johaa1993/PDB/PDB5/address_1.PNG

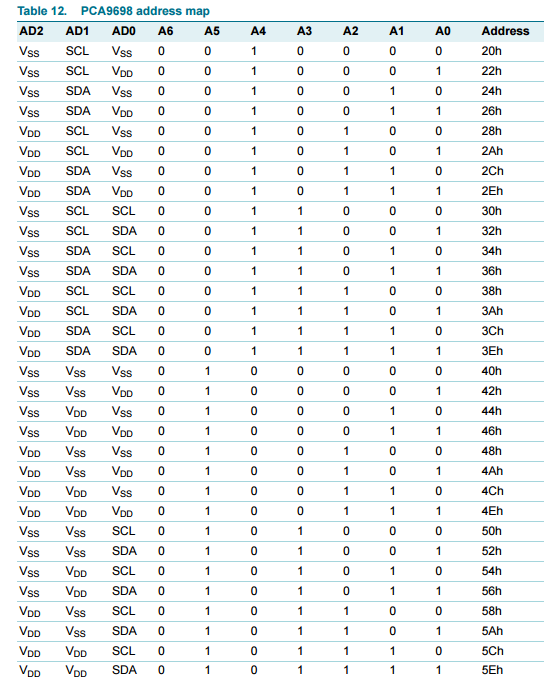
PDB5/address_1.PNG
