johaa1993/PDB/PDB5/Capture2.PNG

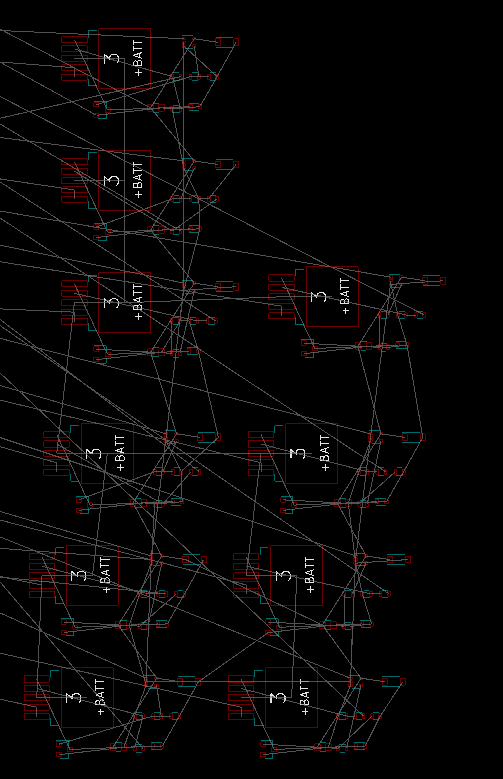
PDB5/Capture2.PNG
