johaa1993/PDB/PDB5/Capture.PNG

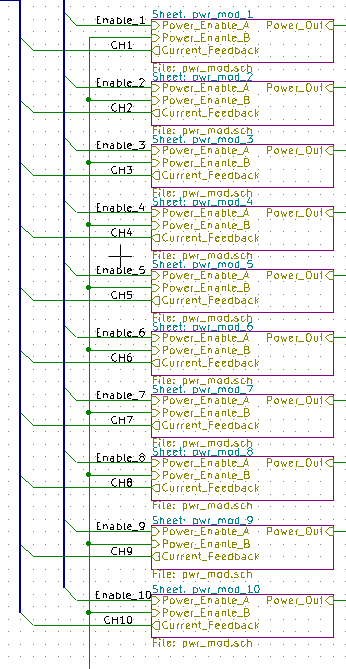
PDB5/Capture.PNG
