johaa1993/PDB/AUIPS7111S/main.kicad_pcb

## KiCad design AUIPS7111S/main.kicad_pcb (2016-11-23)

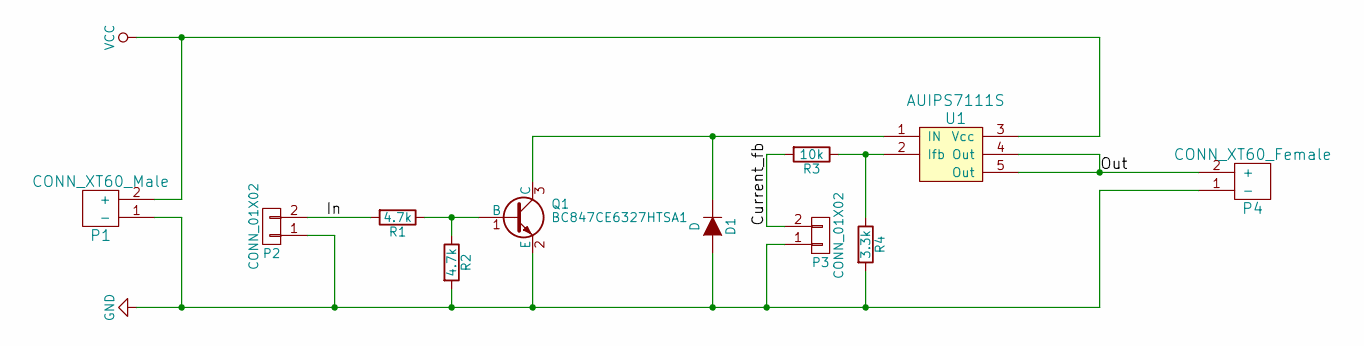
[picture p43: schematic main.sch]

Parts:
D1: D; Diode_DO-35_SOD27_Horizontal_RM10
P1: CONN_XT60_Male; CONN_XT60_Male1_Horizontal
P2, P3: CONN_01X02; Pin_Header_Straight_1x02
P4: CONN_XT60_Female; CONN_XT60_Female_Horizontal
Q1: BC847CE6327HTSA1; SOT-23
R1, R2: 4.7k; Resistor_Horizontal_RM7mm
R3: 10k; Resistor_Horizontal_RM7mm
R4: 3.3k; Resistor_Horizontal_RM7mm
U1: AUIPS7111S; TO-263-5Lead

Connections:
/Current_fb: P3.2, R3.2
/In: P2.2, R1.2
/Out: P4.2 (+), U1.4 (Out), U1.5 (Out)
GND: D1.2 (A), P1.1 (-), P2.1, P3.1, P4.1 (-), Q1.2 (E), R2.2, R4.2
unnamed: D1.1 (K), Q1.3 (C), U1.1 (IN)
unnamed: Q1.1 (B), R1.1, R2.1
unnamed: R3.1, R4.1, U1.2 (Ifb)
VCC: P1.2 (+), U1.3 (Vcc)

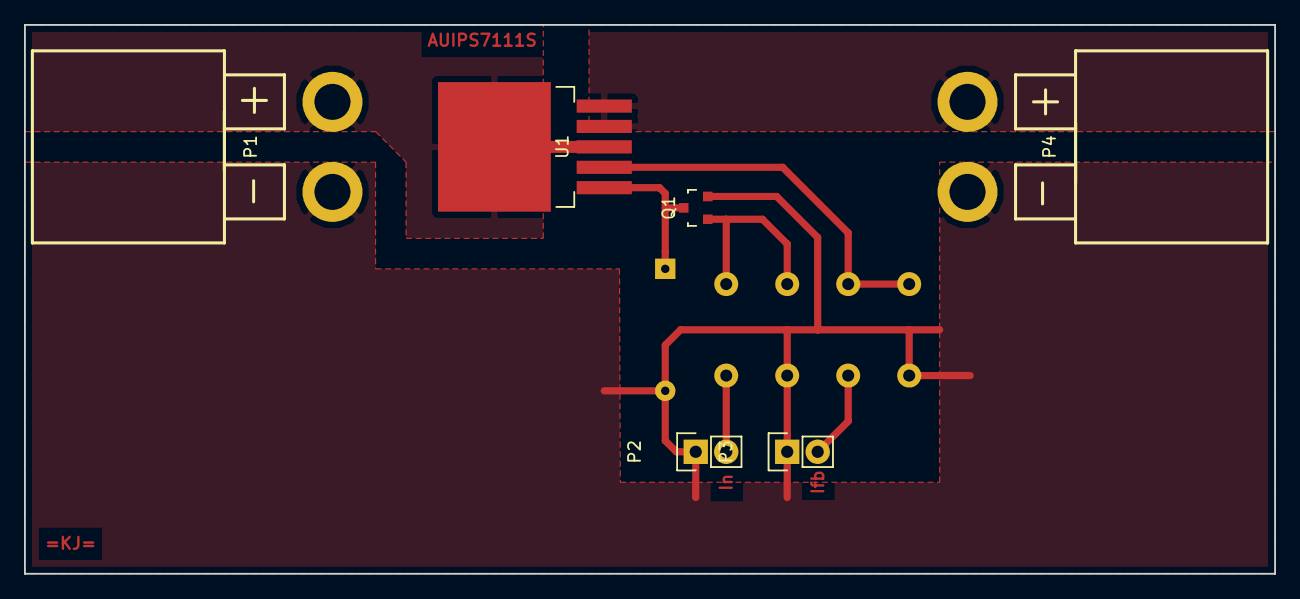
[picture p44: board AUIPS7111S/main.kicad_pcb from above]

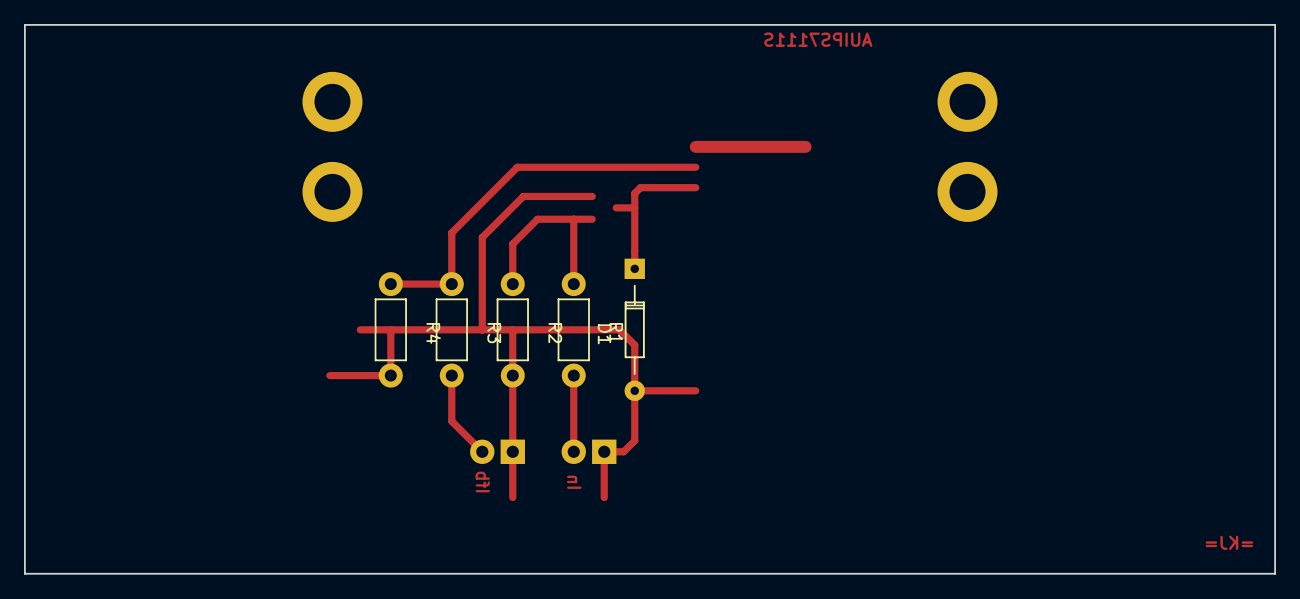
[picture p45: board AUIPS7111S/main.kicad_pcb from below]

Board: 2 copper layers, 104.1 x 45.7 mm, 11 parts (5 on the bottom side), 8 nets.
