johaa1993/PDB/pdb3/main.kicad_pcb

## KiCad design pdb3/main.kicad_pcb (2016-11-21)

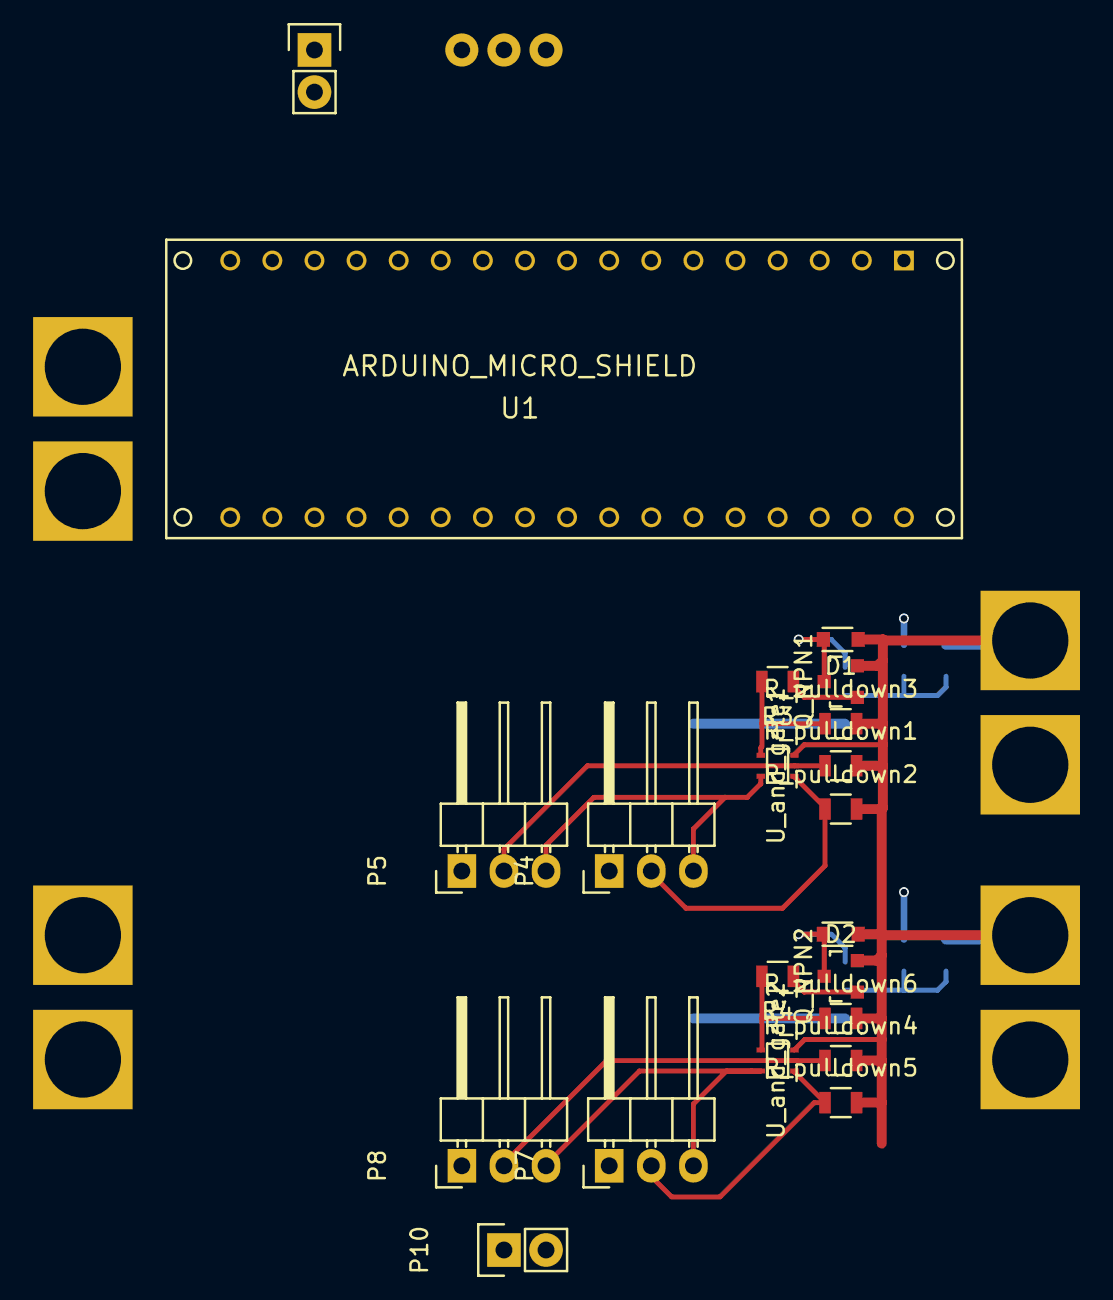
[picture p46: board pdb3/main.kicad_pcb from above]

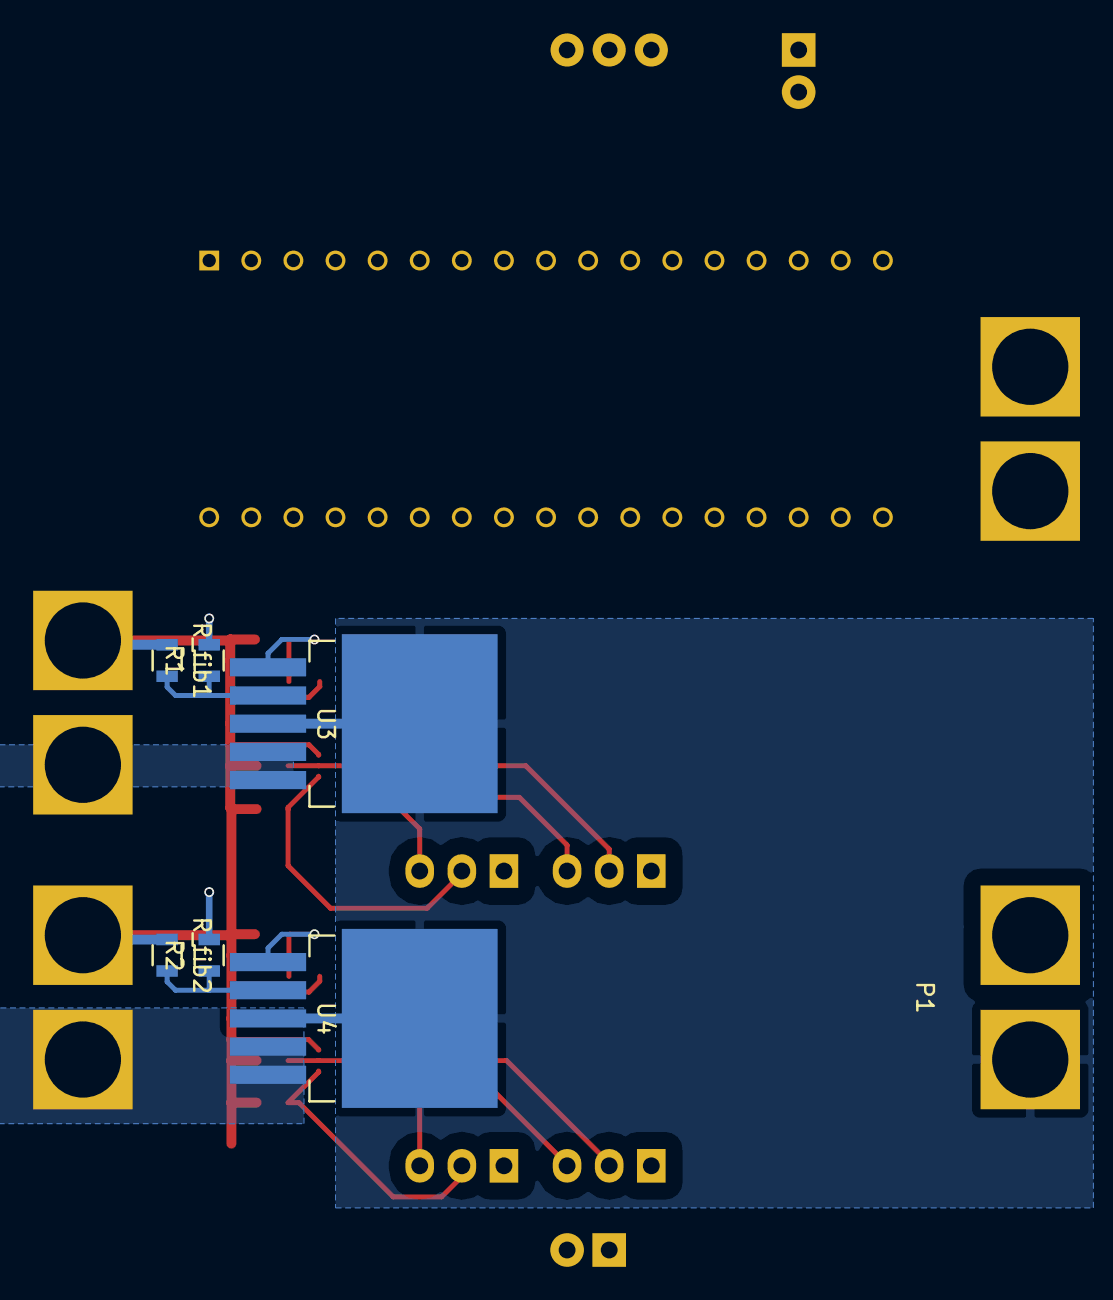
[picture p47: board pdb3/main.kicad_pcb from below]

Board: 4 copper layers, 32 parts (8 on the bottom side), 24 nets.

Parts:
D1, D2: D_Small; D_0805
P1, P2: CONN_XT60_Male; XT60
P3: CONN_01X02; Pin_Header_Straight_1x02
P4, P5, P7, P8: CONN_01X03; Pin_Header_Angled_1x03
P6, P9: CONN_XT60_Female; XT60
P10: CONN_01X02_Reed; Pin_Header_Straight_1x02
Q_NPN1, Q_NPN2: BC849; SOT-23
R1, R2: 10k; R_0805
R3, R4: 5k; R_0805
R_fib1, R_fib2: R; R_0805
R_pulldown1, R_pulldown2, R_pulldown3, R_pulldown4, R_pulldown5, R_pulldown6: 5k; R_0805
U1: ARDUINO_MICRO_SHIELD
U2: WPMDH1100501S; WPMDH1100xx1S
U3, U4: AUIPS7111S; TO-263-5Lead
U_and_gate1, U_and_gate2: 74LVC1G08; SOT-353

Connections:
/A0: R1.2, U1.A0
/A1: R2.2, U1.A1
/Arduino_3.3V: P4.3, P5.3, P7.3, P8.3, P10.2, U1.3.3V, U_and_gate1.5, U_and_gate2.5
/Enable0: P4.1, U1.13
/Enable1: P7.1, U1.5
/KSW1/AUIPS7111S_IN: D1.1, Q_NPN1.3, U3.1
/KSW1/Out: P6.2, U3.4, U3.5
/KSW2/AUIPS7111S_IN: D2.1, Q_NPN2.3, U4.1
/KSW2/Out: P9.2, U4.4, U4.5
GND: D1.2, D2.2, P1.2, P2.2, P3.1, P6.1, P9.1, Q_NPN1.2, Q_NPN2.2, R_fib1.1, R_fib2.1, R_pulldown1.2, R_pulldown2.2, R_pulldown3.2, R_pulldown4.2, R_pulldown5.2, R_pulldown6.2, U1.GND, U2.2, U_and_gate1.3, U_and_gate2.3
unnamed: P3.2, U2.3
unnamed: P4.2, R_pulldown2.1, U_and_gate1.1
unnamed: P5.2, R_pulldown1.1, U_and_gate1.2
unnamed: P7.2, R_pulldown5.1, U_and_gate2.1
unnamed: P8.2, R_pulldown4.1, U_and_gate2.2
unnamed: Q_NPN1.1, R3.1
unnamed: Q_NPN2.1, R4.1
unnamed: R1.1, R_fib1.2, U3.2
unnamed: R2.1, R_fib2.2, U4.2
unnamed: R3.2, R_pulldown3.1, U_and_gate1.4
unnamed: R4.2, R_pulldown6.1, U_and_gate2.4
Reed: P5.1, P8.1, P10.1
VCC_7..12V: P2.1, U1.VI
VCC_8..50V: P1.1, U3.3, U4.3
