johaa1993/PDB/pdb4/pdb1.kicad_pcb

## KiCad design pdb4/pdb1.kicad_pcb (2016-11-20)

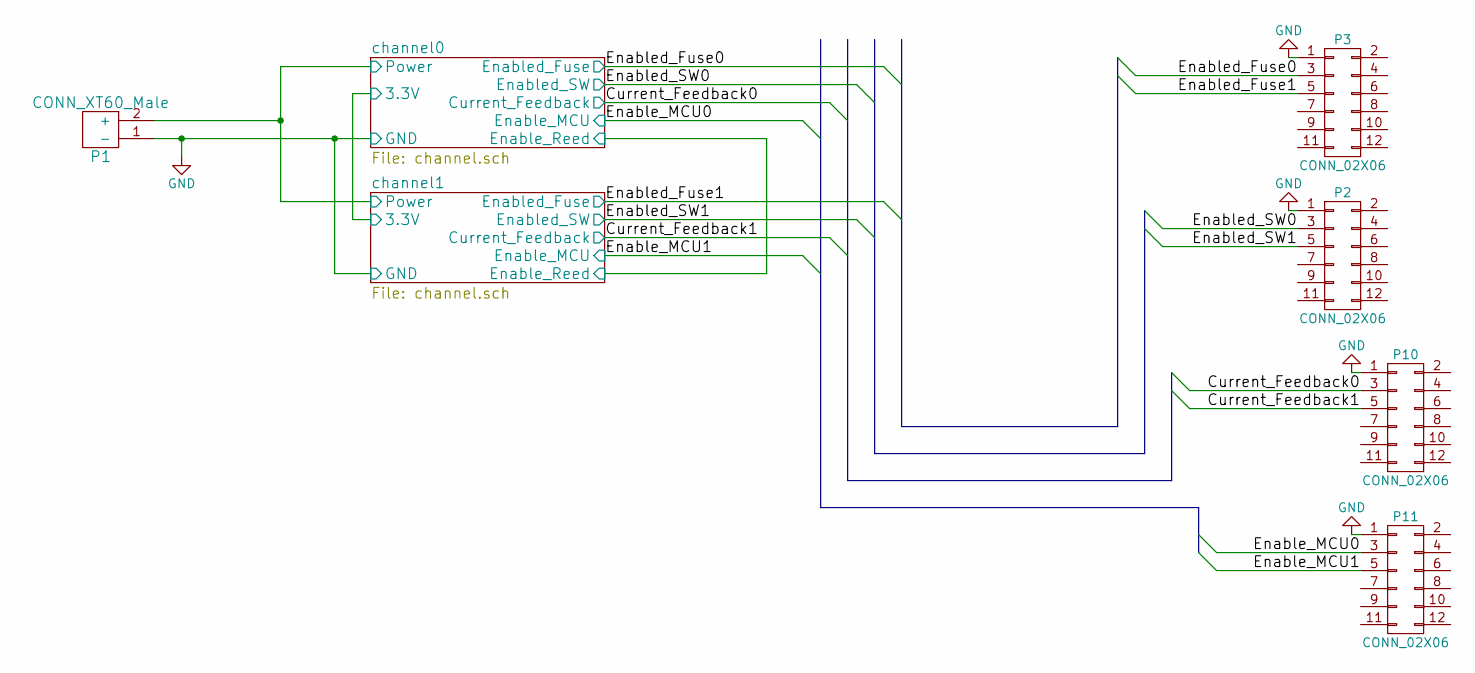
[picture p48: schematic pdb1.sch]

Parts:
P1: CONN_XT60_Male; CONN_XT60_Male_Horizontal
P2, P3, P10, P11: CONN_02X06; Pin_Header_Straight_2x06

Connections:
/Current_Feedback0: P10.3; also elsewhere on the board
/Current_Feedback1: P10.5; also elsewhere on the board
/Enable_MCU0: P11.3; also elsewhere on the board
/Enable_MCU1: P11.5; also elsewhere on the board
/Enabled_Fuse0: P3.3; also elsewhere on the board
/Enabled_Fuse1: P3.5; also elsewhere on the board
/Enabled_SW0: P2.3; also elsewhere on the board
/Enabled_SW1: P2.5; also elsewhere on the board
/channel0/Power: P1.2 (+); also elsewhere on the board
GND: P1.1 (-), P2.1, P3.1, P10.1, P11.1; also elsewhere on the board

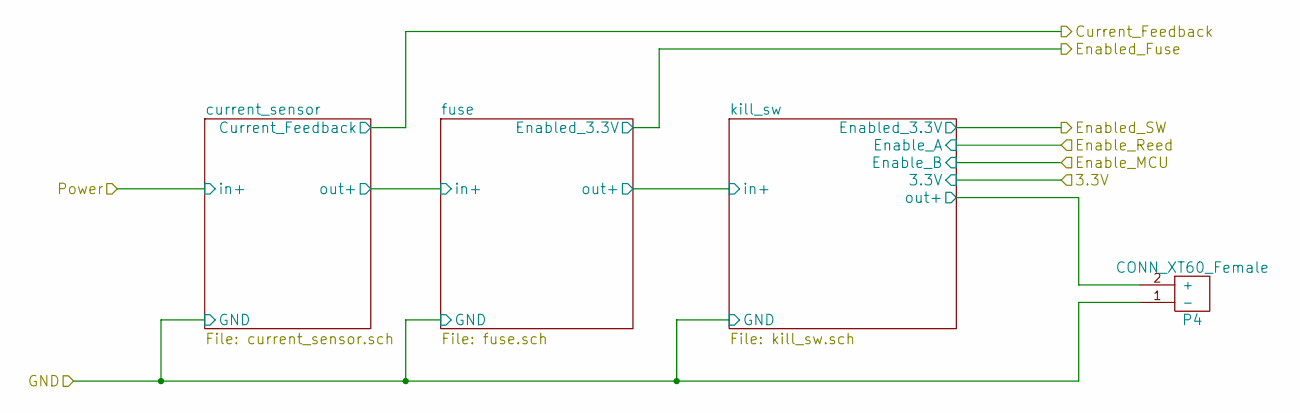
[picture p49: schematic channel.sch]

Parts:
P4: CONN_XT60_Female; CONN_XT60_Female_Horizontal

Connections:
/channel0/kill_sw/out+: P4.2 (+); also elsewhere on the board
GND: P4.1 (-); also elsewhere on the board

Parts of its further copies:
P7: CONN_XT60_Female; CONN_XT60_Female_Horizontal

Connections of its further copies:
/channel1/kill_sw/out+: P7.2 (+); also elsewhere on the board
GND: P7.1 (-); also elsewhere on the board

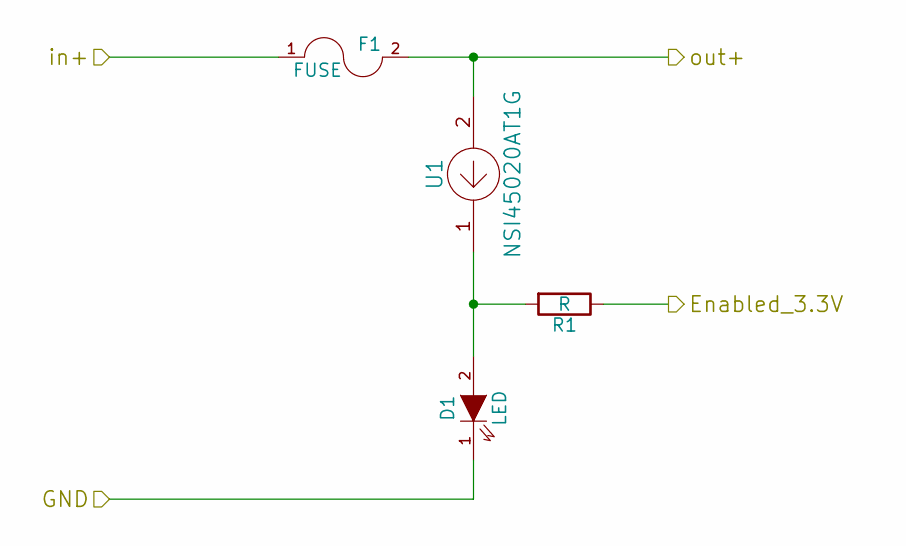
[picture p50: schematic fuse.sch]

Parts:
D1: LED; LED_0805
F1: FUSE; Fuseholder_test
R1: R; R_0805
U1: NSI45020AT1G; SOD-123

Connections:
/Enabled_Fuse0: R1.1; also elsewhere on the board
/channel0/fuse/in+: F1.1; also elsewhere on the board
/channel0/kill_sw/in+: F1.2, U1.2; also elsewhere on the board
GND: D1.1 (K); also elsewhere on the board
unnamed: D1.2 (A), R1.2, U1.1

Parts of its further copies:
D3: LED; LED_0805
F2: FUSE; Fuseholder_test
R8: R; R_0805
U6: NSI45020AT1G; SOD-123

Connections of its further copies:
/Enabled_Fuse1: R8.1; also elsewhere on the board
/channel1/fuse/in+: F2.1; also elsewhere on the board
/channel1/kill_sw/in+: F2.2, U6.2; also elsewhere on the board
GND: D3.1 (K); also elsewhere on the board
unnamed: D3.2 (A), R8.2, U6.1

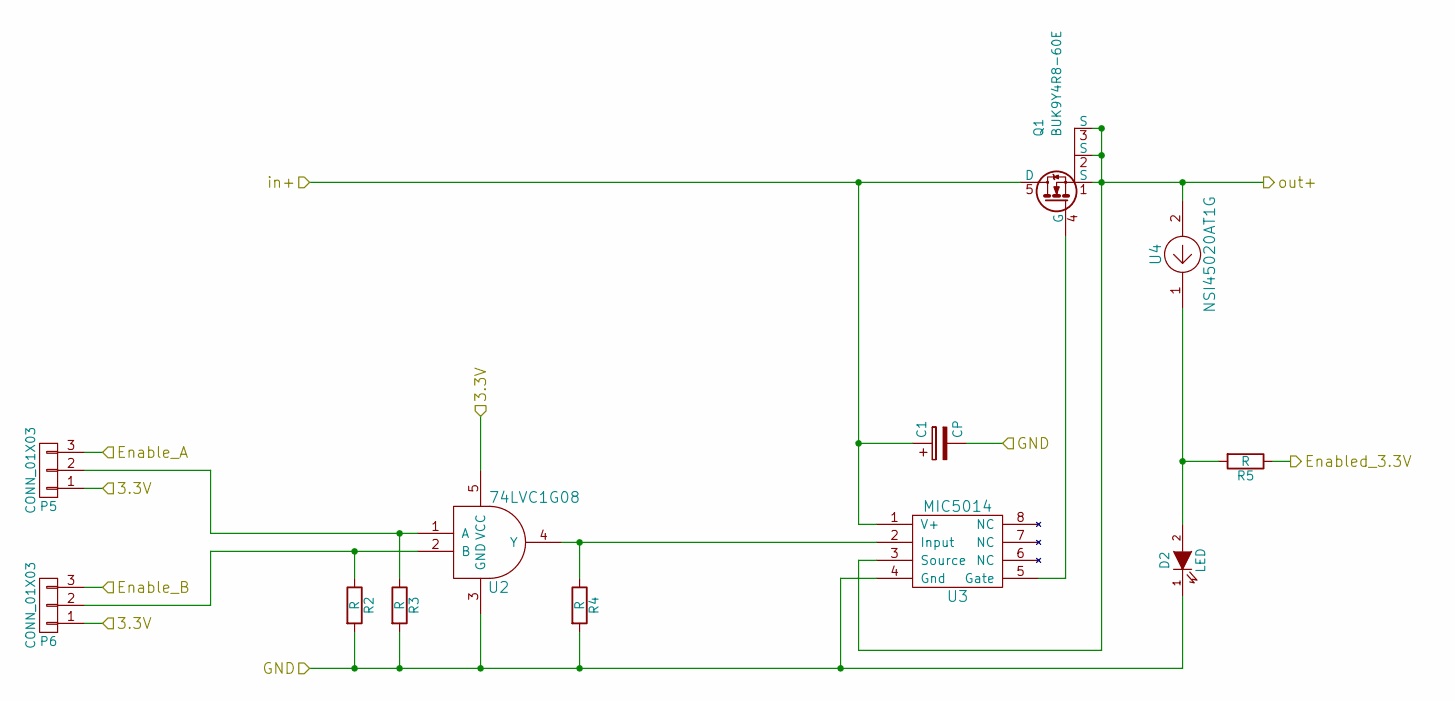
[picture p51: schematic kill_sw.sch]

Parts:
C1: CP; c_elec_4x4.5
D2: LED; LED_0805
P5, P6: CONN_01X03; Pin_Header_Straight_1x03
Q1: BUK9Y4R8-60E; SOT-669_LFPAK
R2, R3, R4, R5: R; R_0805
U2: 74LVC1G08; SOT-353
U3: MIC5014; SOIC-8_3.9x4.9mm_Pitch1.27mm
U4: NSI45020AT1G; SOD-123

Connections:
/Enable_MCU0: P6.3; also elsewhere on the board
/Enabled_SW0: R5.1; also elsewhere on the board
/channel0/3.3V: P5.1, P6.1, U2.5 (VCC)
/channel0/Enable_Reed: P5.3; also elsewhere on the board
/channel0/kill_sw/in+: C1.1, Q1.5 (D), U3.1 (V+); also elsewhere on the board
/channel0/kill_sw/out+: Q1.1 (S), Q1.2 (S), Q1.3 (S), U3.3 (Source), U4.2; also elsewhere on the board
GND: C1.2, D2.1 (K), R2.2, R3.2, R4.2, U2.3 (GND), U3.4 (Gnd); also elsewhere on the board
unnamed: D2.2 (A), R5.2, U4.1
unnamed: P5.2, R3.1, U2.1 (A)
unnamed: P6.2, R2.1, U2.2 (B)
unnamed: Q1.4 (G), U3.5 (Gate)
unnamed: R4.1, U2.4 (Y), U3.2 (Input)

Parts of its further copies:
C4: CP; c_elec_4x4.5
D4: LED; LED_0805
P8, P9: CONN_01X03; Pin_Header_Straight_1x03
Q2: BUK9Y4R8-60E; SOT-669_LFPAK
R9, R10, R11, R12: R; R_0805
U7: 74LVC1G08; SOT-353
U8: MIC5014; SOIC-8_3.9x4.9mm_Pitch1.27mm
U9: NSI45020AT1G; SOD-123

Connections of its further copies:
/Enable_MCU1: P9.3; also elsewhere on the board
/Enabled_SW1: R12.1; also elsewhere on the board
/channel0/Enable_Reed: P8.3; also elsewhere on the board
/channel1/3.3V: P8.1, P9.1, U7.5 (VCC)
/channel1/kill_sw/in+: C4.1, Q2.5 (D), U8.1 (V+); also elsewhere on the board
/channel1/kill_sw/out+: Q2.1 (S), Q2.2 (S), Q2.3 (S), U8.3 (Source), U9.2; also elsewhere on the board
GND: C4.2, D4.1 (K), R9.2, R10.2, R11.2, U7.3 (GND), U8.4 (Gnd); also elsewhere on the board
unnamed: D4.2 (A), R12.2, U9.1
unnamed: P8.2, R10.1, U7.1 (A)
unnamed: P9.2, R9.1, U7.2 (B)
unnamed: Q2.4 (G), U8.5 (Gate)
unnamed: R11.1, U7.4 (Y), U8.2 (Input)

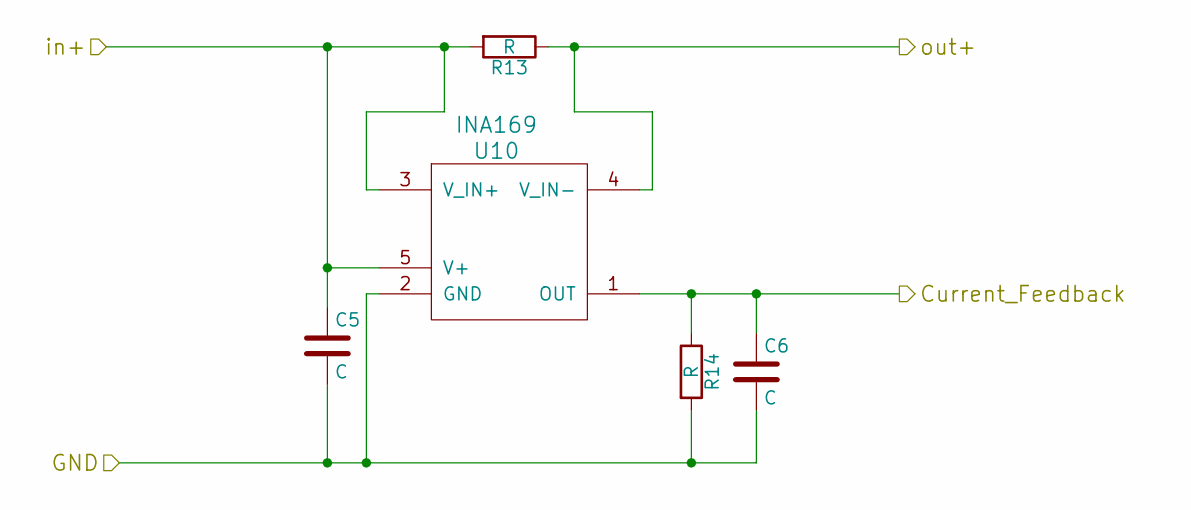
[picture p52: schematic current_sensor.sch]

Parts:
C2, C3: C; C_0805
R6: R; SMD_1052_Metric
R7: R; R_0805
U5: INA169; SOT-23-5

Connections:
/Current_Feedback0: C3.1, R7.1, U5.1 (OUT); also elsewhere on the board
/channel0/Power: C2.1, R6.2, U5.3 (V_IN+), U5.5 (V+); also elsewhere on the board
/channel0/fuse/in+: R6.1, U5.4 (V_IN-); also elsewhere on the board
GND: C2.2, C3.2, R7.2, U5.2 (GND); also elsewhere on the board

Parts of its further copies:
C5, C6: C; C_0805
R13: R; SMD_1052_Metric
R14: R; R_0805
U10: INA169; SOT-23-5

Connections of its further copies:
/Current_Feedback1: C6.1, R14.1, U10.1 (OUT); also elsewhere on the board
/channel0/Power: C5.1, R13.2, U10.3 (V_IN+), U10.5 (V+); also elsewhere on the board
/channel1/fuse/in+: R13.1, U10.4 (V_IN-); also elsewhere on the board
GND: C5.2, C6.2, R14.2, U10.2 (GND); also elsewhere on the board

Board: 4 copper layers, 49 parts (4 on the bottom side), 31 nets, no tracks yet.
