johaa1993/PDB/pdb2/pdb1.kicad_pcb

## KiCad design pdb2/pdb1.kicad_pcb (2016-11-18, an earlier design)

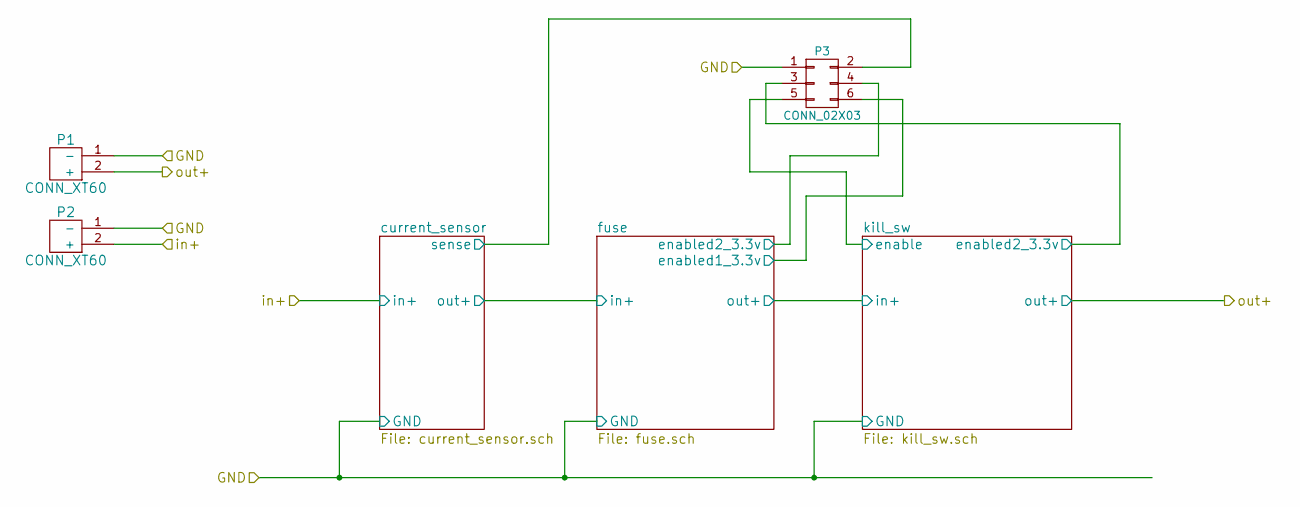
[picture p53: schematic channel.sch]

Parts:
P1: CONN_XT60; XT60_Horizontal1
P2: CONN_XT60; XT60_Horizontal2
P3: CONN_02X03; Pin_Header_Straight_2x03_box

Connections:
/channel/GND: P1.1 (-), P2.1 (-), P3.1; also elsewhere on the board
/channel/current_sensor/sense: P3.2; also elsewhere on the board
/channel/fuse/enabled1_3.3v: P3.6; also elsewhere on the board
/channel/fuse/enabled2_3.3v: P3.4; also elsewhere on the board
/channel/in+: P2.2 (+); also elsewhere on the board
/channel/kill_sw/enable: P3.5; also elsewhere on the board
/channel/kill_sw/enabled2_3.3v: P3.3; also elsewhere on the board
/channel/out+: P1.2 (+); also elsewhere on the board

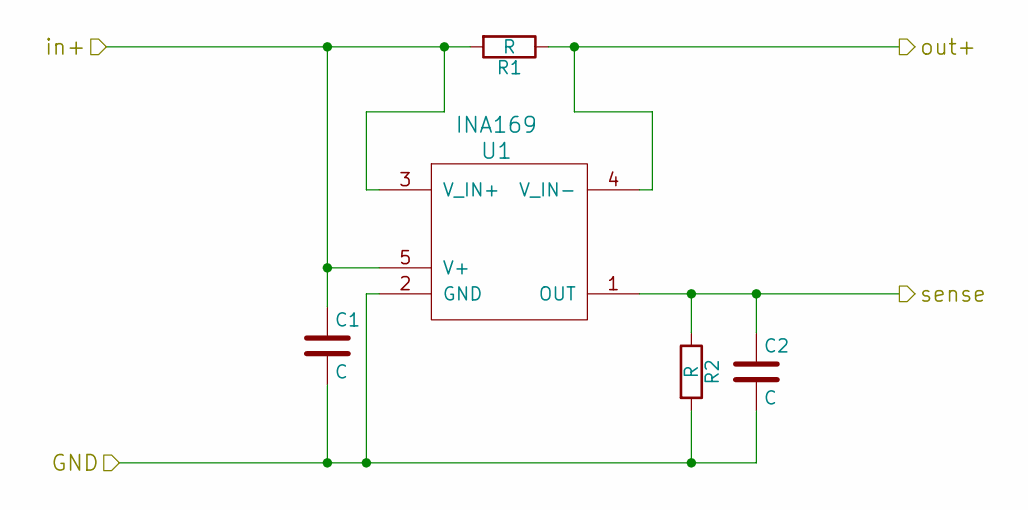
[picture p54: schematic current_sensor.sch]

Parts:
C1, C2: C; C_0603
R1: R; SMD_1052_Metric
R2: R; R_0603
U1: INA169; SOT-23-5

Connections:
/channel/GND: C1.2, C2.2, R2.2, U1.2 (GND); also elsewhere on the board
/channel/current_sensor/sense: C2.1, R2.1, U1.1 (OUT); also elsewhere on the board
/channel/fuse/in+: R1.1, U1.4 (V_IN-); also elsewhere on the board
/channel/in+: C1.1, R1.2, U1.3 (V_IN+), U1.5 (V+); also elsewhere on the board

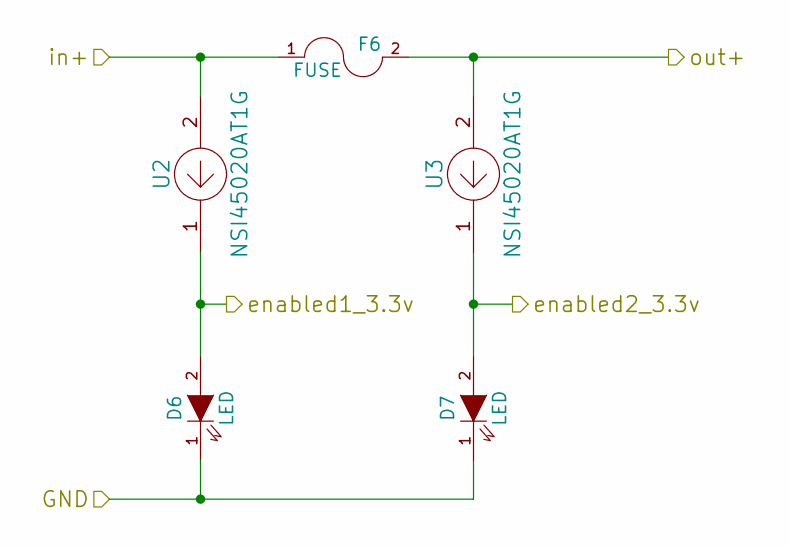
[picture p55: schematic fuse.sch]

Parts:
D6, D7: LED; LED_0805
F6: FUSE; Fuseholder_test
U2, U3: NSI45020AT1G; SOD-123

Connections:
/channel/GND: D6.1 (K), D7.1 (K); also elsewhere on the board
/channel/fuse/enabled1_3.3v: D6.2 (A), U2.1; also elsewhere on the board
/channel/fuse/enabled2_3.3v: D7.2 (A), U3.1; also elsewhere on the board
/channel/fuse/in+: F6.1, U2.2; also elsewhere on the board
/channel/kill_sw/in+: F6.2, U3.2; also elsewhere on the board

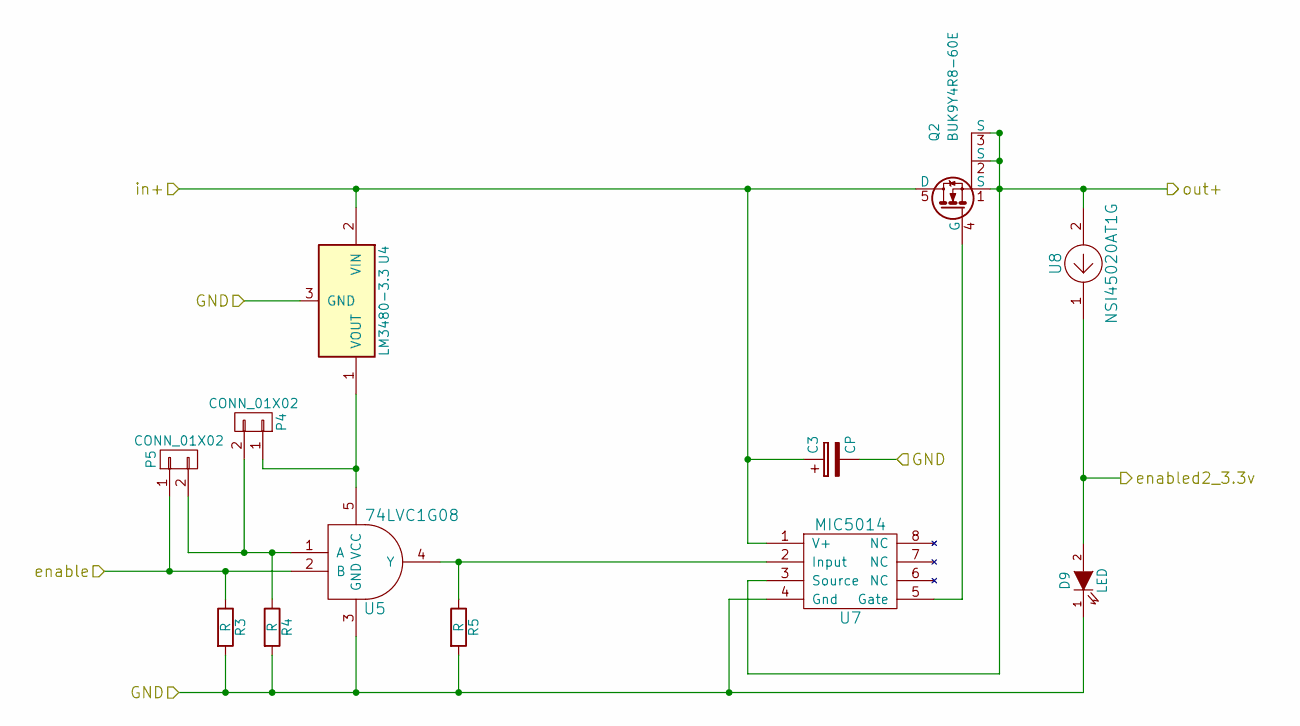
[picture p56: schematic kill_sw.sch]

Parts:
C3: CP; C_Axial_D5_L11_P18
D9: LED; LED_0805
P4, P5: CONN_01X02; Pin_Header_Straight_1x02
Q2: BUK9Y4R8-60E; SOT-669_LFPAK
R3, R4, R5: R; R_0603
U4: LM3480-3.3; SOT-23
U5: 74LVC1G08; SOT-353
U7: MIC5014; SOIC-8_3.9x4.9mm_Pitch1.27mm
U8: NSI45020AT1G; SOD-123

Connections:
/channel/GND: C3.2, D9.1 (K), R3.2, R4.2, R5.2, U4.3 (GND), U5.3 (GND), U7.4 (Gnd); also elsewhere on the board
/channel/kill_sw/enable: P5.1, R3.1, U5.2 (B); also elsewhere on the board
/channel/kill_sw/enabled2_3.3v: D9.2 (A), U8.1; also elsewhere on the board
/channel/kill_sw/in+: C3.1, Q2.5 (D), U4.2 (VIN), U7.1 (V+); also elsewhere on the board
/channel/out+: Q2.1 (S), Q2.2 (S), Q2.3 (S), U7.3 (Source), U8.2; also elsewhere on the board
unnamed: P4.1, U4.1 (VOUT), U5.5 (VCC)
unnamed: P4.2, P5.2, R4.1, U5.1 (A)
unnamed: Q2.4 (G), U7.5 (Gate)
unnamed: R5.1, U5.4 (Y), U7.2 (Input)

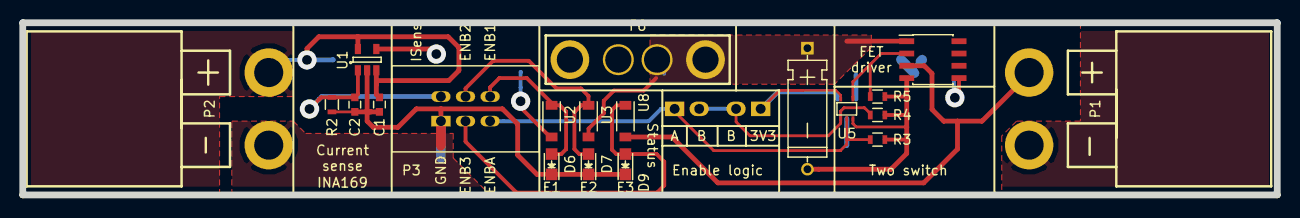
[picture p57: board pdb2/pdb1.kicad_pcb from above]

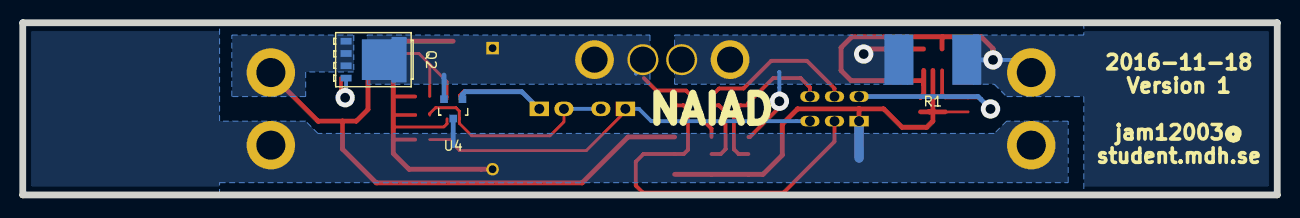
[picture p58: board pdb2/pdb1.kicad_pcb from below]

Board: 2 copper layers, 129.5 x 17.8 mm, 25 parts (3 on the bottom side), 14 nets.
