johaa1993/PDB/LTC6802-2/main.kicad_pcb

## KiCad design LTC6802-2/main.kicad_pcb (2016-11-18)

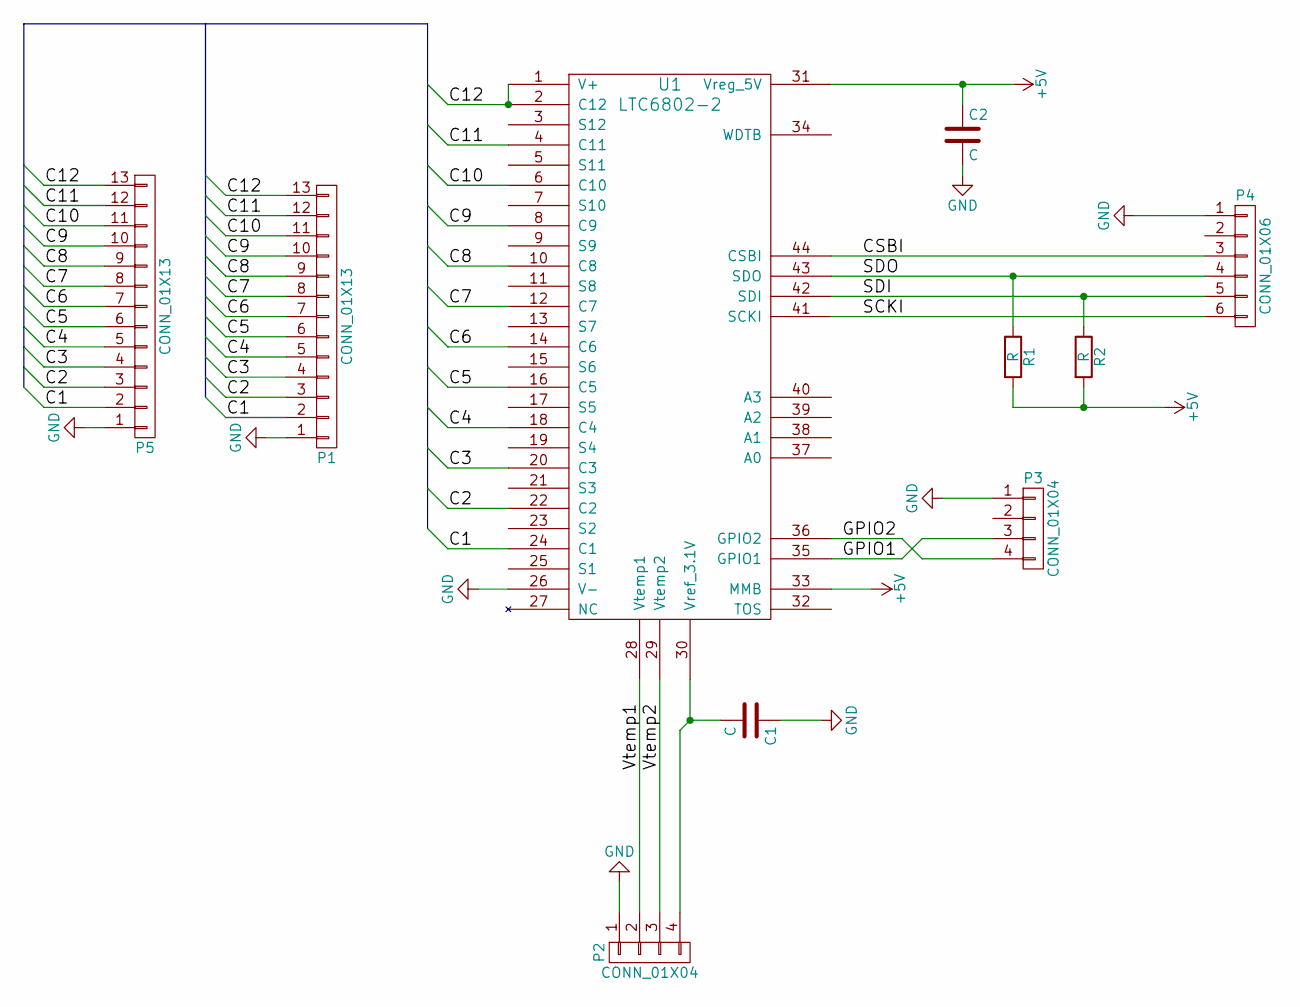
[picture p59: schematic main.sch]

Parts:
C1, C2: C; C_0805
P1, P5: CONN_01X13; Pin_Header_Straight_1x13
P2, P3: CONN_01X04; Pin_Header_Straight_1x04
P4: CONN_01X06; Pin_Header_Straight_1x06
R1, R2: R; R_0805
U1: LTC6802-2; SSOP-44

Connections:
+5V: C2.1, R1.2, R2.2, U1.31 (Vreg_5V), U1.33 (MMB)
/C1: P1.2, P5.2, U1.24 (C1)
/C2: P1.3, P5.3, U1.22 (C2)
/C3: P1.4, P5.4, U1.20 (C3)
/C4: P1.5, P5.5, U1.18 (C4)
/C5: P1.6, P5.6, U1.16 (C5)
/C6: P1.7, P5.7, U1.14 (C6)
/C7: P1.8, P5.8, U1.12 (C7)
/C8: P1.9, P5.9, U1.10 (C8)
/C9: P1.10, P5.10, U1.8 (C9)
/C10: P1.11, P5.11, U1.6 (C10)
/C11: P1.12, P5.12, U1.4 (C11)
/C12: P1.13, P5.13, U1.1 (V+), U1.2 (C12)
/CSBI: P4.3, U1.44 (CSBI)
/GPIO1: P3.3, U1.35 (GPIO1)
/GPIO2: P3.4, U1.36 (GPIO2)
/SCKI: P4.6, U1.41 (SCKI)
/SDI: P4.5, R2.1, U1.42 (SDI)
/SDO: P4.4, R1.1, U1.43 (SDO)
/Vtemp1: P2.2, U1.28 (Vtemp1)
/Vtemp2: P2.3, U1.29 (Vtemp2)
GND: C1.1, C2.2, P1.1, P2.1, P3.1, P4.1, P5.1, U1.26 (V-)
unnamed: C1.2, P2.4, U1.30 (Vref_3.1V)

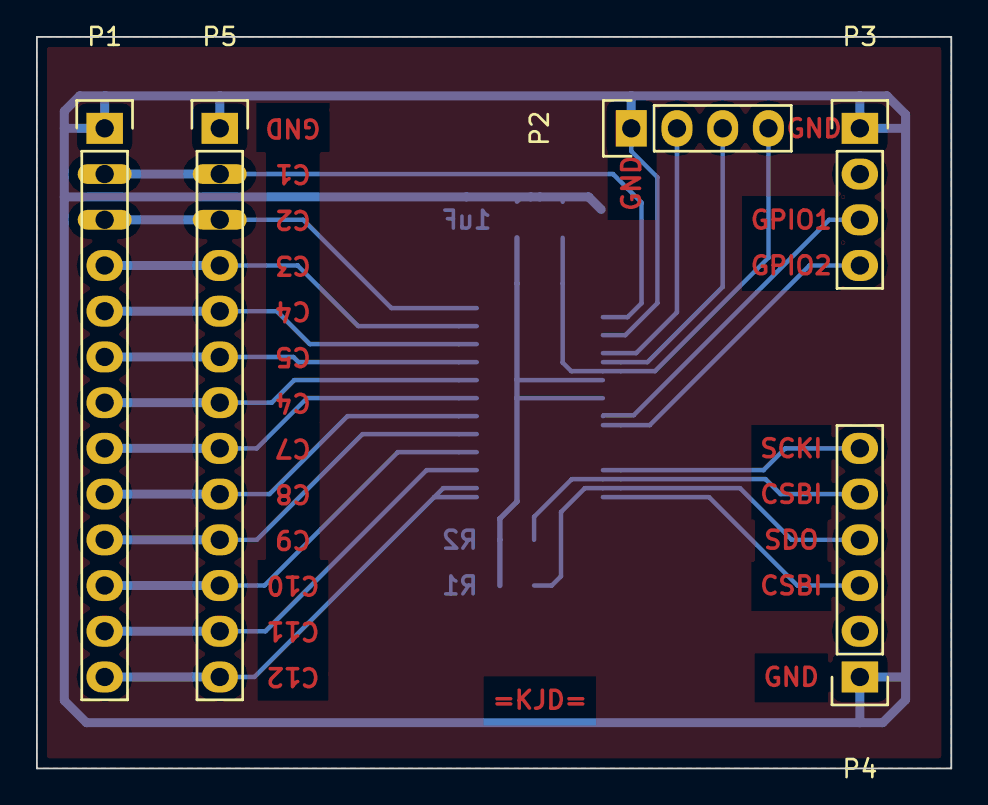
[picture p60: board LTC6802-2/main.kicad_pcb from above]

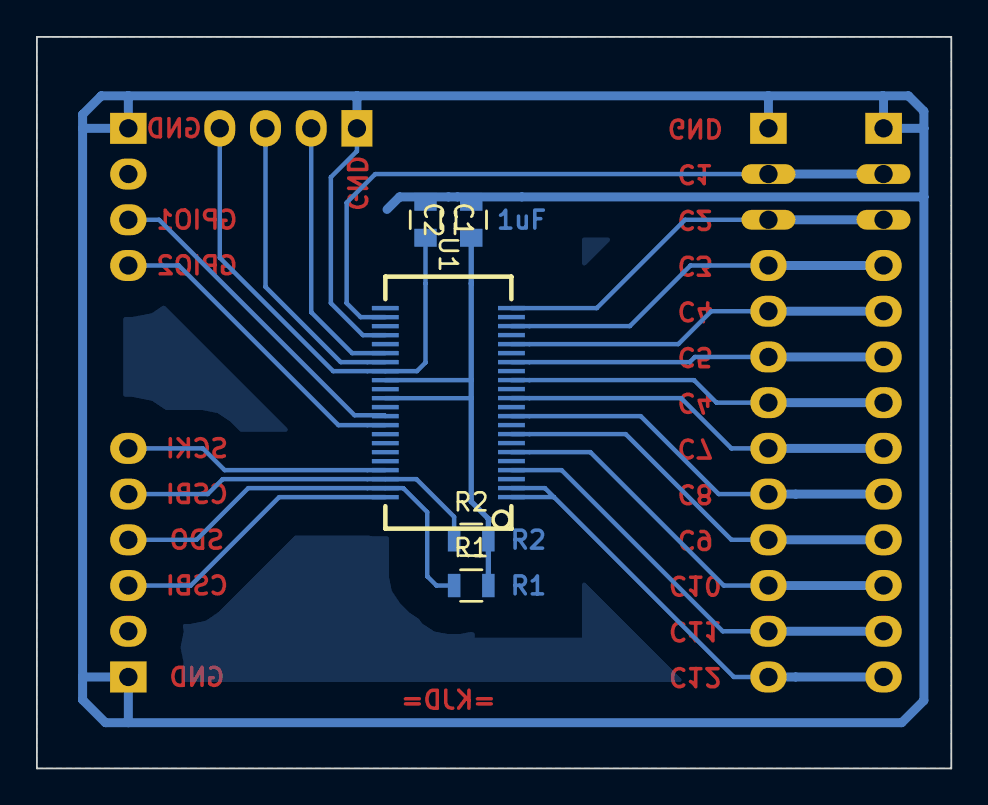
[picture p61: board LTC6802-2/main.kicad_pcb from below]

Board: 2 copper layers, 50.8 x 40.6 mm, 10 parts (5 on the bottom side), 23 nets.
