johaa1993/PDB/ksw/main.kicad_pcb

## KiCad design ksw/main.kicad_pcb (2016-11-12)

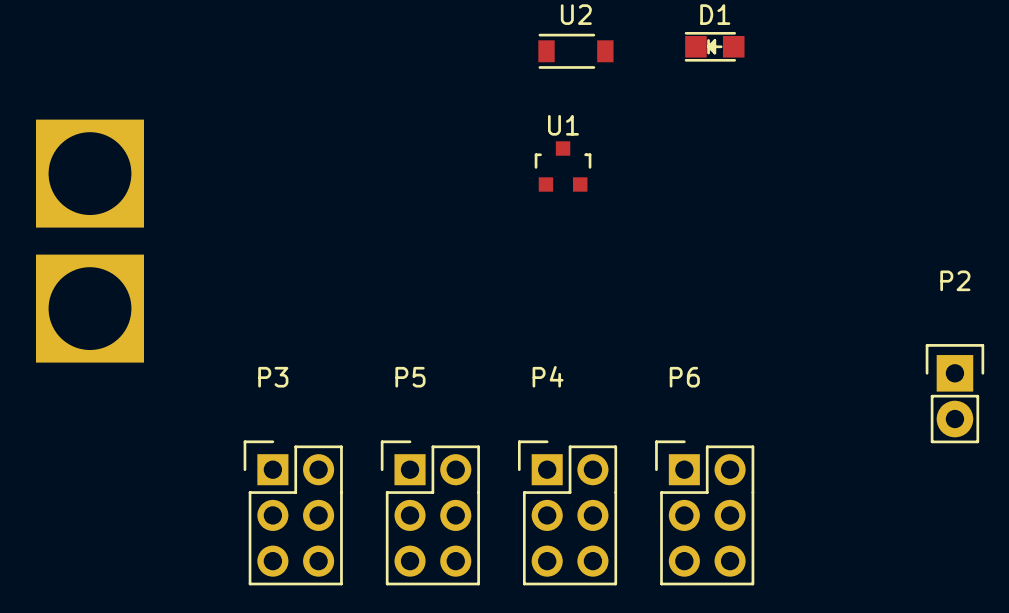
[picture p62: board ksw/main.kicad_pcb from above]

Board: 2 copper layers, 9 parts (0 on the bottom side), 5 nets, no tracks yet.

Parts:
D1: 3.3v; LED_0805
P1: CONN_XT60; XT60
P2: CONN_01X02; Pin_Header_Straight_1x02
P3, P4, P5, P6: CONN_02X03; Pin_Header_Straight_2x03
U1: LM3480-3.3; SOT-23
U2: NSI45020AT1G; SOD-123

Connections:
+3V3: P3.6, P4.6, P5.6, P6.6, U1.1
/GND: D1.1, P1.1, P3.1, P4.1, P5.1, P6.1, U1.3
/In+: P1.2, U1.2, U2.2
unnamed: D1.2, P2.2, U2.1
unnamed: P2.1, P3.5, P4.5, P5.5, P6.5
