johaa1993/PDB/sw_high_side3/main.kicad_pcb

## KiCad design sw_high_side3/main.kicad_pcb (2016-11-09)

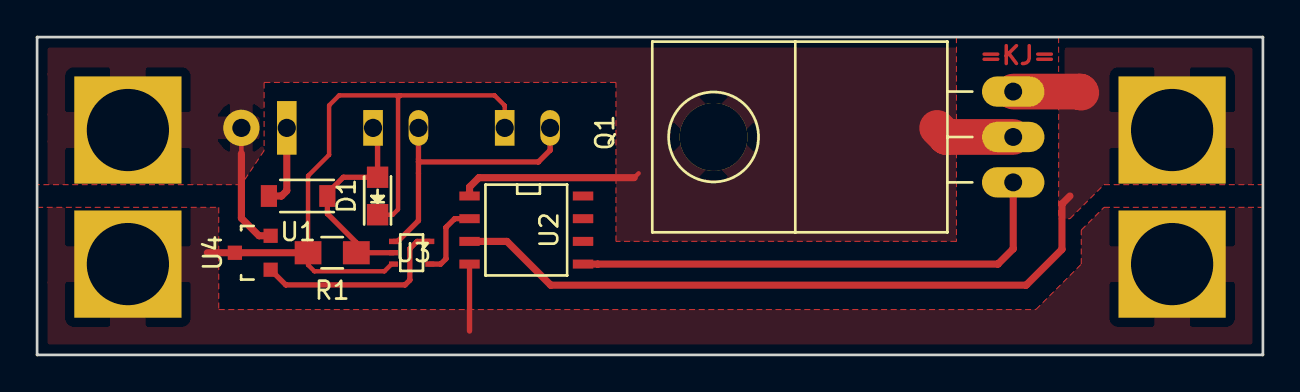
[picture p63: board sw_high_side3/main.kicad_pcb from above]

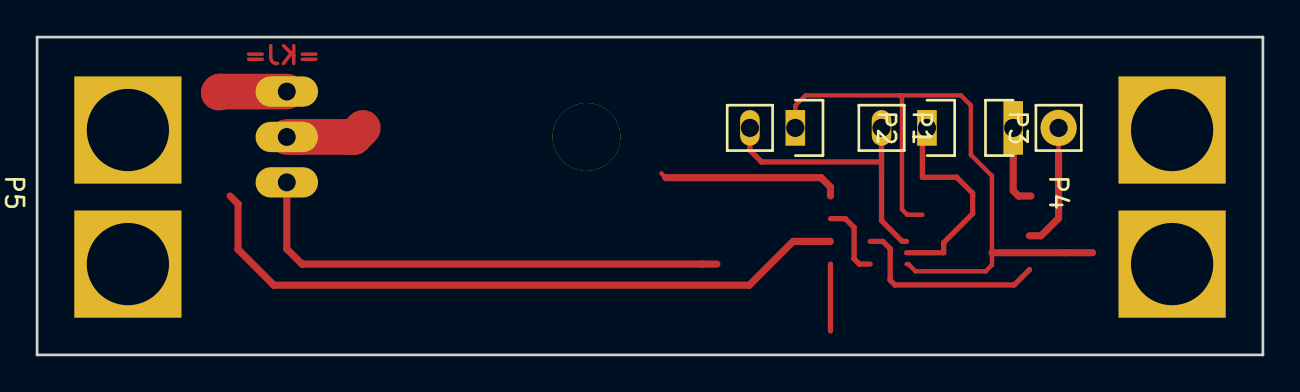
[picture p64: board sw_high_side3/main.kicad_pcb from below]

Board: 2 copper layers, 68.6 x 17.8 mm, 12 parts (5 on the bottom side), 9 nets.

Parts:
D1: 3.3v; LED_0805
P1, P2, P3: CONN_01X02; Pin_Header_Straight_1x02
P4, P5: CONN_XT60; XT60
Q1: IRFB7537PbF; TO-220_Horizontal_LargePads_HeatsinkPad
R1: 10k; R_0805_HandSoldering
U1: NSI45020AT1G; SOD-123
U2: MIC5014; SOIC-8-N
U3: 74LVC1G08; SOT-353
U4: LM3480-3.3; SOT-23

Connections:
/In+: P1.2, P4.2, Q1.2, U2.1, U4.2
/In-: D1.1, P2.1, P4.1, P5.1, R1.2, U2.4, U3.3, U4.3
/Out+: P5.2, Q1.3, U2.3
unnamed: D1.2, P3.1, R1.1, U1.1, U3.2
unnamed: P1.1, U1.2
unnamed: P2.2, P3.2, U3.1
unnamed: Q1.1, U2.5
unnamed: U2.2, U3.4
unnamed: U3.5, U4.1
