johaa1993/PDB/74LVC1G08GW/main.kicad_pcb

## KiCad design 74LVC1G08GW/main.kicad_pcb (2016-11-08)

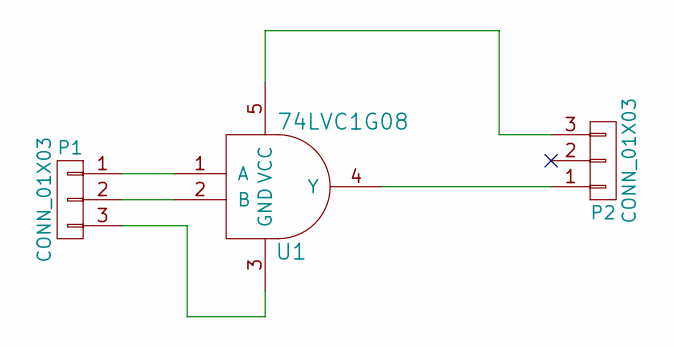
[picture p65: schematic main.sch]

Parts:
P1, P2: CONN_01X03; Pin_Header_Straight_1x03
U1: 74LVC1G08; SOT-353

Connections:
unnamed: P1.1, U1.1 (A)
unnamed: P1.2, U1.2 (B)
unnamed: P1.3, U1.3 (GND)
unnamed: P2.1, U1.4 (Y)
unnamed: P2.3, U1.5 (VCC)

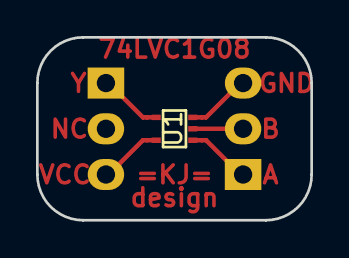
[picture p66: board 74LVC1G08GW/main.kicad_pcb from above]

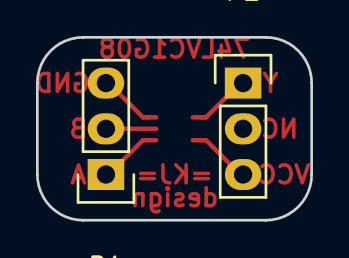
[picture p67: board 74LVC1G08GW/main.kicad_pcb from below]

Board: 2 copper layers, 15.2 x 10.2 mm, 3 parts (2 on the bottom side), 5 nets.
