johaa1993/PDB/NSI45020AT1G/main.kicad_pcb

## KiCad design NSI45020AT1G/main.kicad_pcb (2016-11-08)

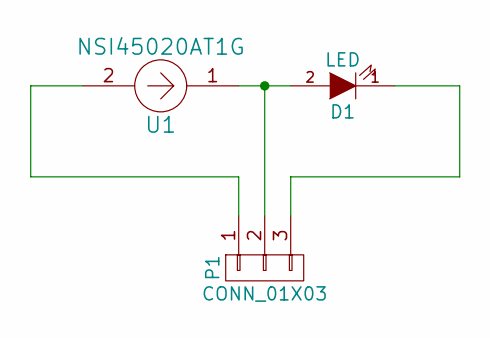
[picture p68: schematic main.sch]

Parts:
D1: LED; LED_0805
P1: CONN_01X03; Pin_Header_Angled_1x03
U1: NSI45020AT1G; SOD-123

Connections:
unnamed: D1.1 (K), P1.3
unnamed: D1.2 (A), P1.2, U1.1
unnamed: P1.1, U1.2

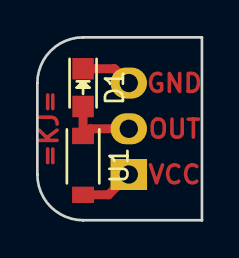
[picture p69: board NSI45020AT1G/main.kicad_pcb from above]

Board: 2 copper layers, 9.1 x 10.2 mm, 3 parts (1 on the bottom side), 3 nets.
