johaa1993/PDB/sw_high_side2/main.kicad_pcb

## KiCad design sw_high_side2/main.kicad_pcb (2016-11-08)

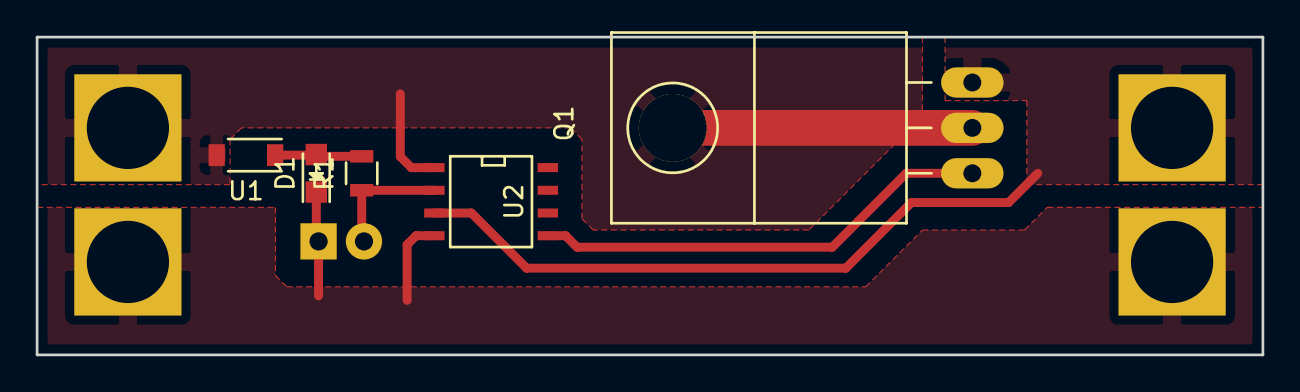
[picture p70: board sw_high_side2/main.kicad_pcb from above]

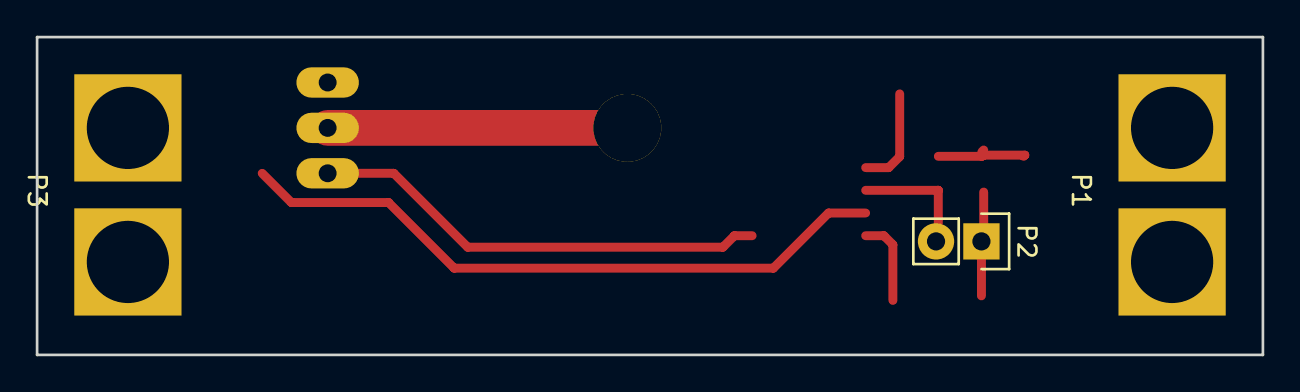
[picture p71: board sw_high_side2/main.kicad_pcb from below]

Board: 2 copper layers, 68.6 x 17.8 mm, 8 parts (3 on the bottom side), 6 nets.

Parts:
D1: LED; LED_0805
P1, P3: CONN_XT60; XT60
P2: CONN_01X02; Pin_Header_Straight_1x02
Q1: IRFB7537PbF; TO-220_Horizontal_LargePads_HeatsinkPad
R1: 10k; R_0805
U1: NSI45020AT1G; SOD-123
U2: MIC5014; SOIC-8-N

Connections:
/In+: P1.2, Q1.2, U1.2, U2.1
/In-: D1.1, P1.1, P2.1, P3.1, U2.4
/Out+: P3.2, Q1.3, U2.3
unnamed: D1.2, R1.2, U1.1
unnamed: P2.2, R1.1, U2.2
unnamed: Q1.1, U2.5
