johaa1993/PDB/MIC5015/main.kicad_pcb

## KiCad design MIC5015/main.kicad_pcb (2016-11-07)

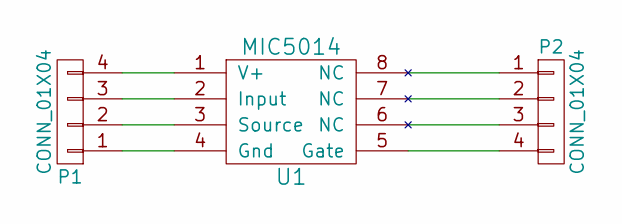
[picture p72: schematic main.sch]

Parts:
P1, P2: CONN_01X04; Pin_Header_Straight_1x04
U1: MIC5014; SOIC-8-N

Connections:
unnamed: P1.1, U1.4 (Gnd)
unnamed: P1.2, U1.3 (Source)
unnamed: P1.3, U1.2 (Input)
unnamed: P1.4, U1.1 (V+)
unnamed: P2.1, U1.8 (NC)
unnamed: P2.2, U1.7 (NC)
unnamed: P2.3, U1.6 (NC)
unnamed: P2.4, U1.5 (Gate)

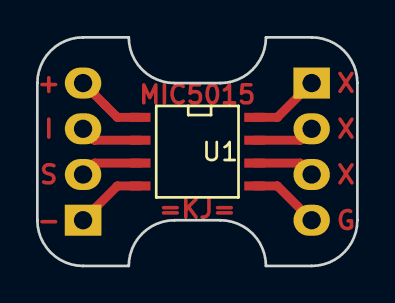
[picture p73: board MIC5015/main.kicad_pcb from above]

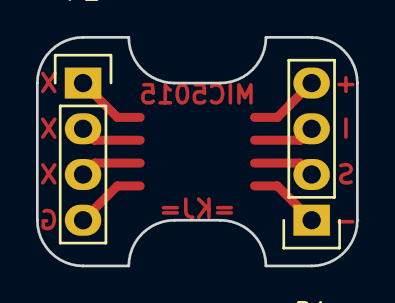
[picture p74: board MIC5015/main.kicad_pcb from below]

Board: 2 copper layers, 17.8 x 12.7 mm, 3 parts (2 on the bottom side), 8 nets.
