johaa1993/PDB/sw_high_side/main.kicad_pcb

## KiCad design sw_high_side/main.kicad_pcb (2016-11-07)

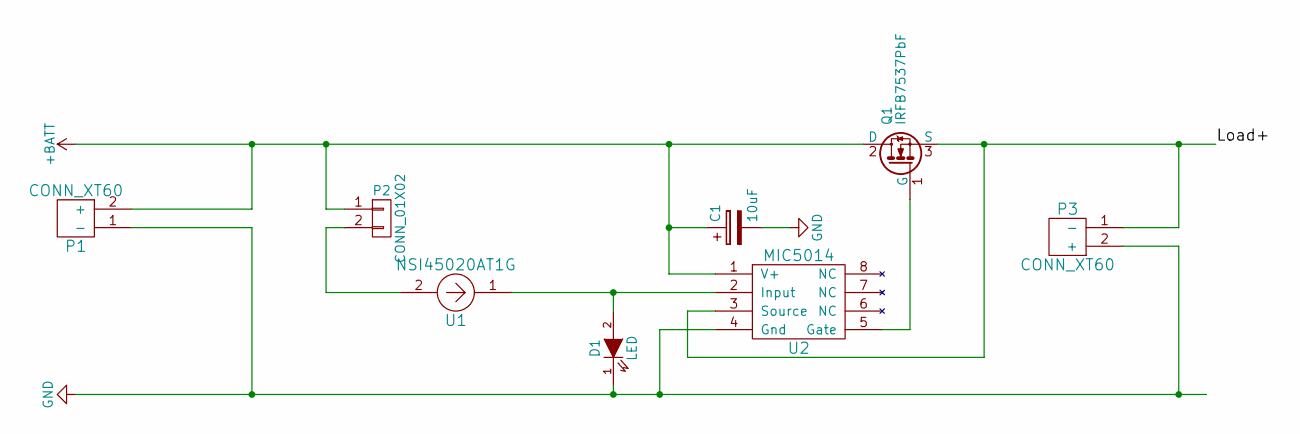
[picture p75: schematic main.sch]

Parts:
C1: 10uF; C_Axial_D5_L11_P18
D1: LED; LED_0805
P1, P3: CONN_XT60; XT60
P2: CONN_01X02; Pin_Header_Straight_1x02
Q1: IRFB7537PbF; TO-220_Horizontal_LargePads_HeatsinkPad
U1: NSI45020AT1G; SOD-123
U2: MIC5014; SOIC-8-N

Connections:
+BATT: C1.1, P1.2 (+), P2.1, Q1.2 (D), U2.1 (V+)
/Load+: P3.1 (-), Q1.3 (S), U2.3 (Source)
GND: C1.2, D1.1 (K), P1.1 (-), P3.2 (+), U2.4 (Gnd)
unnamed: D1.2 (A), U1.1, U2.2 (Input)
unnamed: P2.2, U1.2
unnamed: Q1.1 (G), U2.5 (Gate)

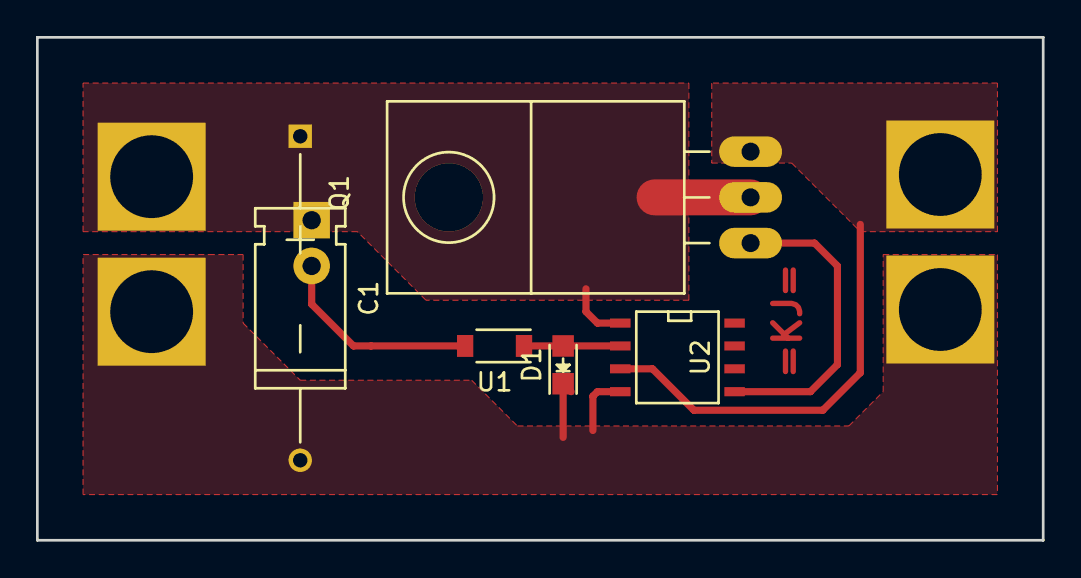
[picture p76: board sw_high_side/main.kicad_pcb from above]

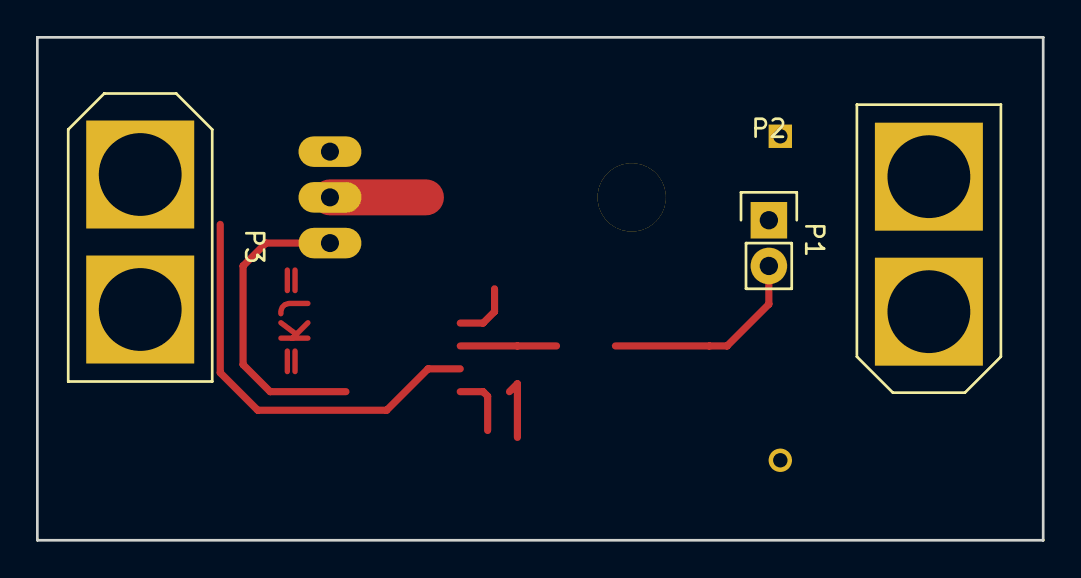
[picture p77: board sw_high_side/main.kicad_pcb from below]

Board: 2 copper layers, 55.9 x 27.9 mm, 8 parts (3 on the bottom side), 6 nets.
