johaa1993/PDB/current_sensor/main.kicad_pcb

## KiCad design current_sensor/main.kicad_pcb (2016-11-04)

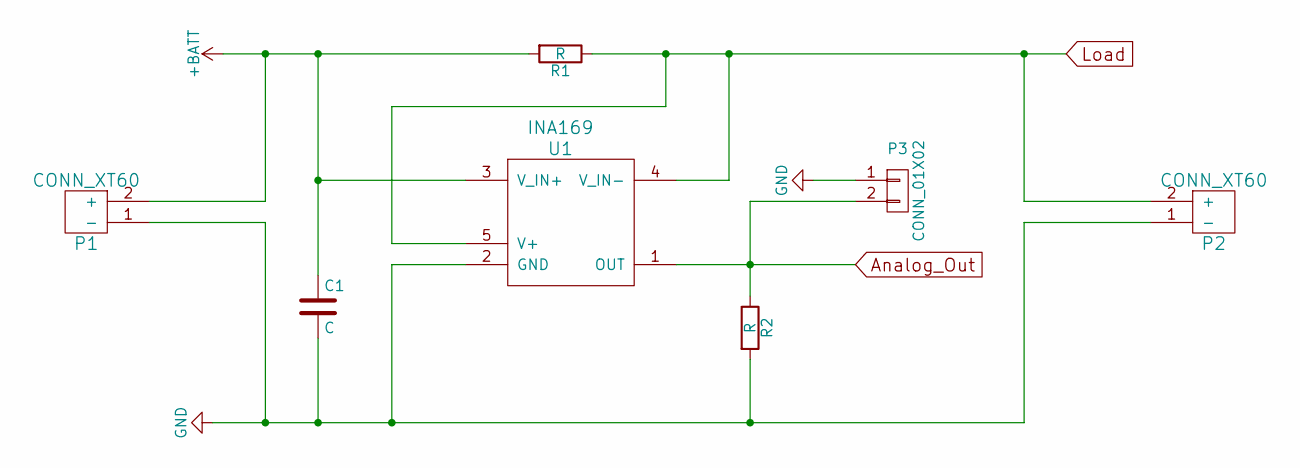
[picture p78: schematic main.sch]

Parts:
C1: C; C_0805_HandSoldering
P1, P2: CONN_XT60; XT60
P3: CONN_01X02; Pin_Header_Straight_1x03
R1: R; SMD_1052_Metric
R2: R; R_0805_HandSoldering
U1: INA169; SOT-23-5

Connections:
+BATT: C1.1, P1.2 (+), R1.2, U1.3 (V_IN+)
Analog_Out: P3.2, R2.1, U1.1 (OUT)
GND: C1.2, P1.1 (-), P2.1 (-), P3.1, R2.2, U1.2 (GND)
Load: P2.2 (+), R1.1, U1.4 (V_IN-), U1.5 (V+)

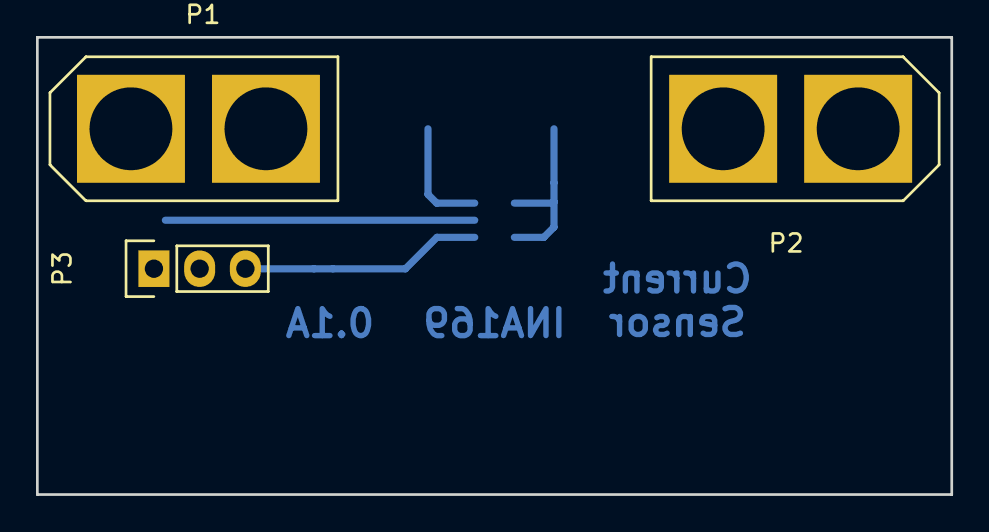
[picture p79: board current_sensor/main.kicad_pcb from above]

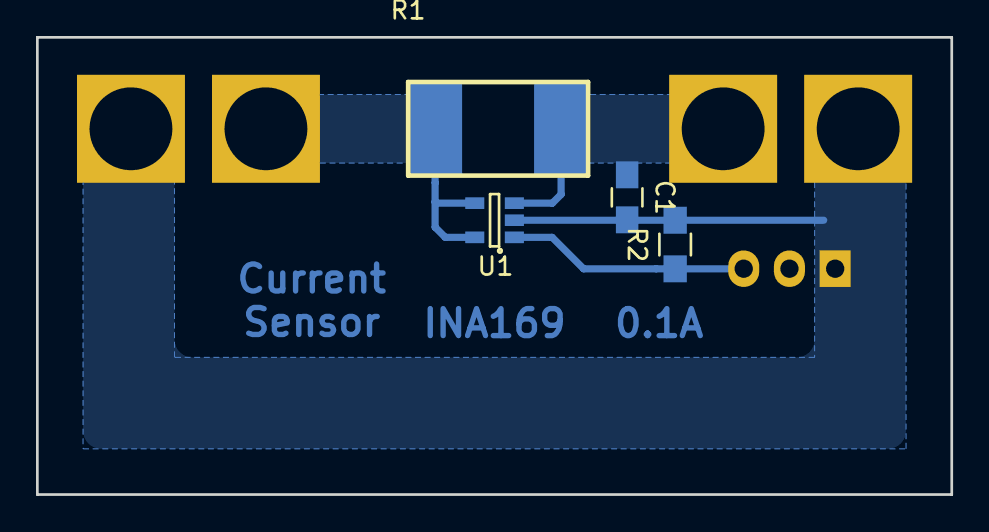
[picture p80: board current_sensor/main.kicad_pcb from below]

Board: 2 copper layers, 50.8 x 25.4 mm, 7 parts (4 on the bottom side), 4 nets.
