johaa1993/PDB/sw_low_side/main.kicad_pcb

## KiCad design sw_low_side/main.kicad_pcb (2016-11-03)

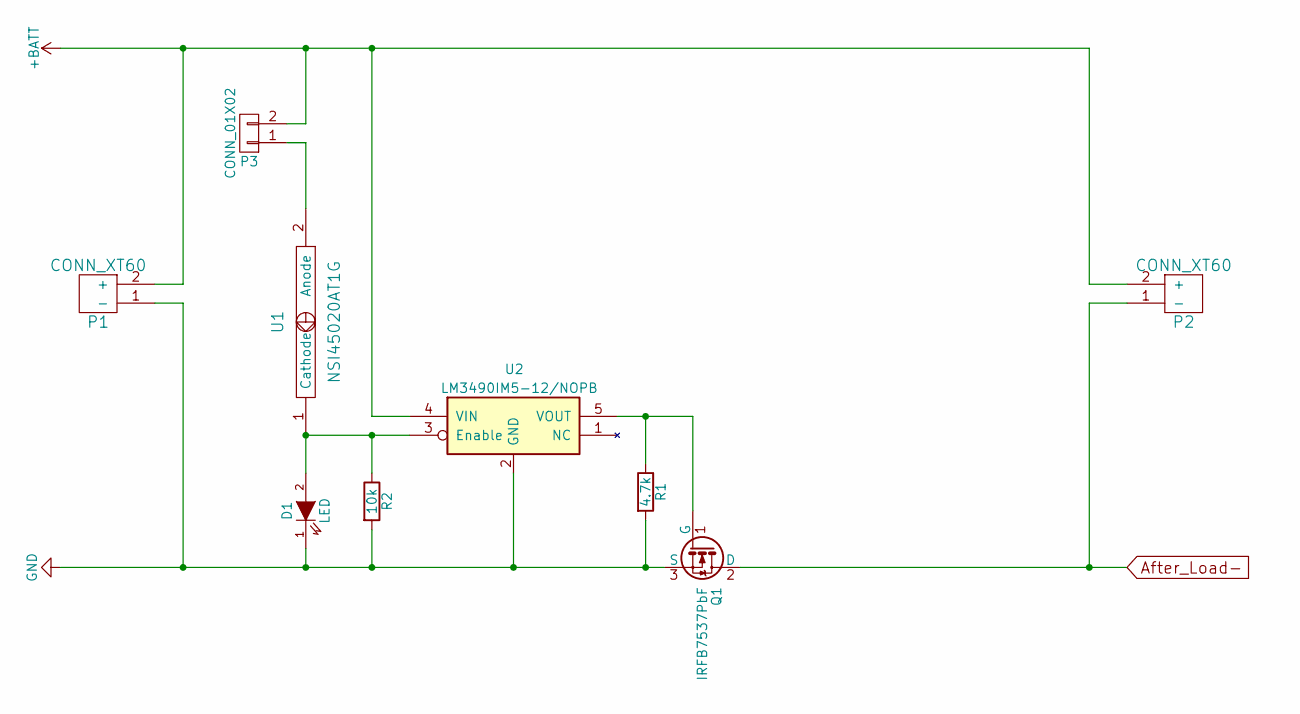
[picture p81: schematic main.sch]

Parts:
D1: LED; LED_0805
P1, P2: CONN_XT60; XT60
P3: CONN_01X02; Pin_Header_Straight_1x02
Q1: IRFB7537PbF; my_TO-220_Neutral123_Horizontal_LargePads
R1: 4.7k; R_0805
R2: 10k; R_0805
U1: NSI45020AT1G; SOD-123
U2: LM3490IM5-12/NOPB; SOT-23-5

Connections:
+BATT: P1.2 (+), P2.2 (+), P3.2, U2.4 (VIN)
After_Load-: P2.1 (-), Q1.2 (D)
GND: D1.1 (K), P1.1 (-), Q1.3 (S), R1.2, R2.2, U2.2 (GND)
unnamed: D1.2 (A), R2.1, U1.1 (Cathode), U2.3 (Enable)
unnamed: P3.1, U1.2 (Anode)
unnamed: Q1.1 (G), R1.1, U2.5 (VOUT)
