johaa1993/PDB/sw_low_side/main.kicad_pcb

## KiCad design sw_low_side/main.kicad_pcb (continued)

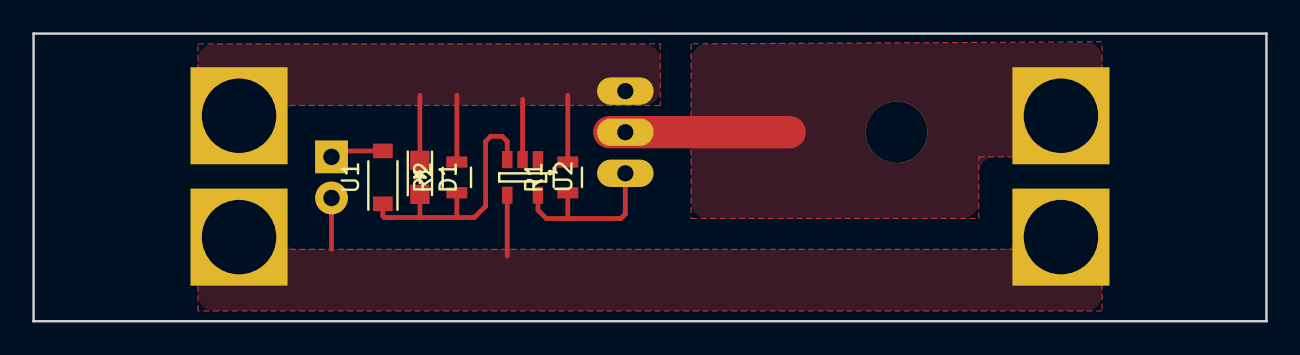
[picture p82: board sw_low_side/main.kicad_pcb from above]

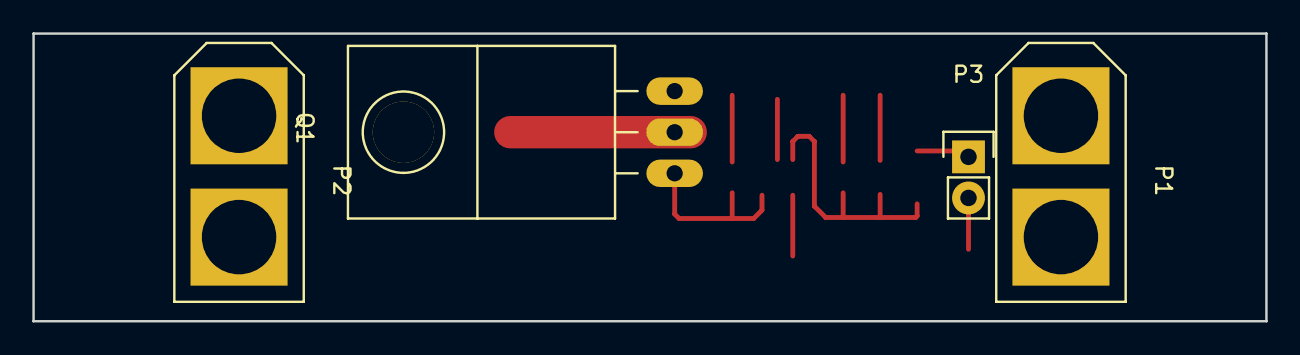
[picture p83: board sw_low_side/main.kicad_pcb from below]

Board: 2 copper layers, 76.2 x 17.8 mm, 9 parts (4 on the bottom side), 6 nets.
